Apologus/openLUXbox/docs/firmware/4Pong/4Pong.jpg

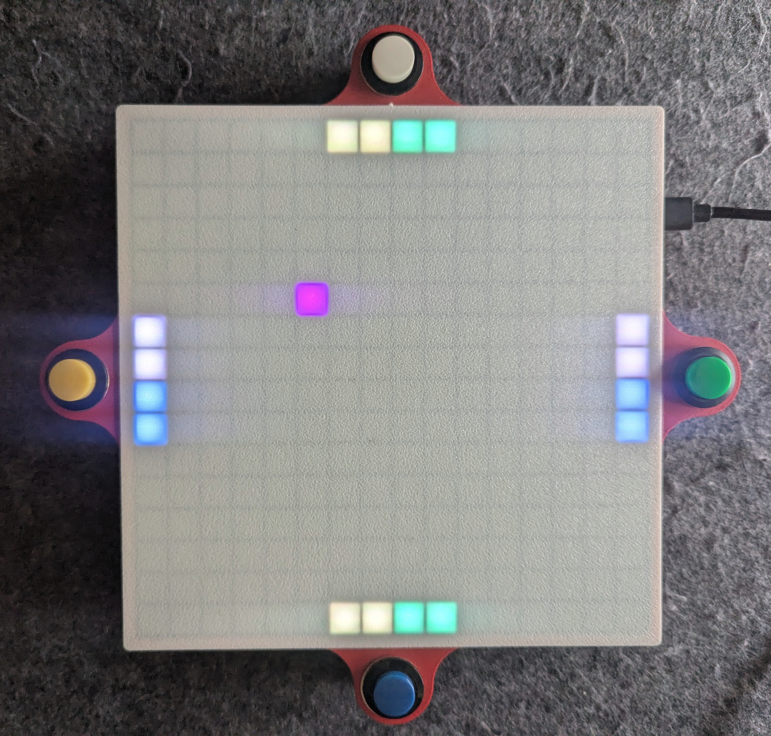
docs/firmware/4Pong/4Pong.jpg
