Apologus/openLUXbox/docs/firmware/canoLbalt/canoLbalt.jpg

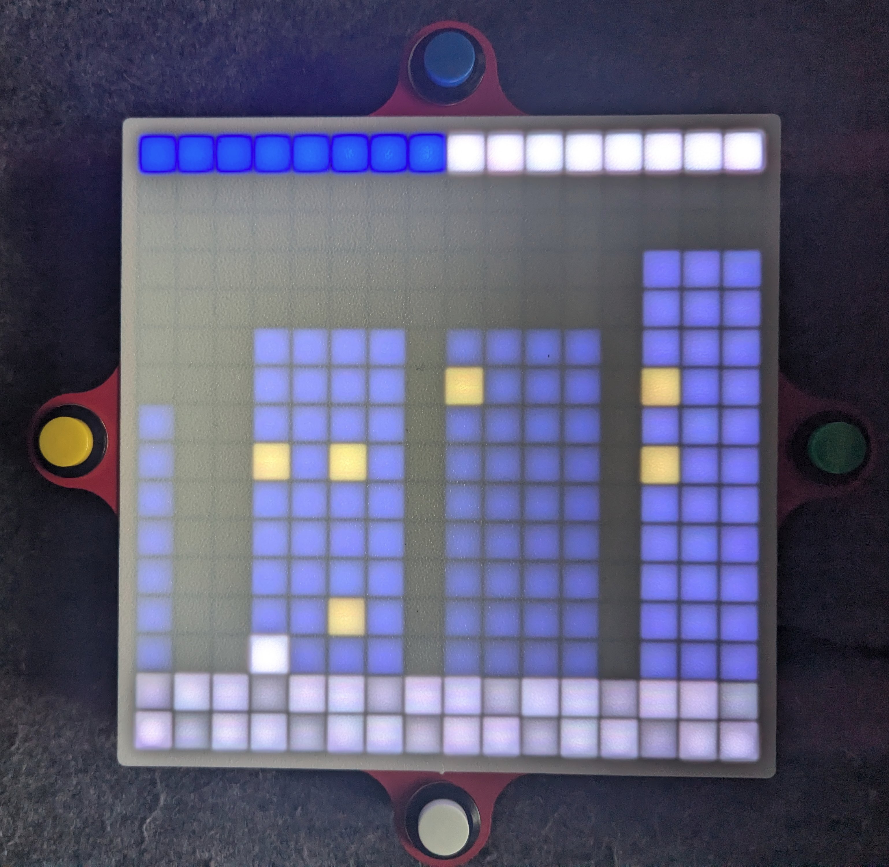
docs/firmware/canoLbalt/canoLbalt.jpg
