Apologus/openLUXbox/docs/firmware/Frog/Frog.jpg

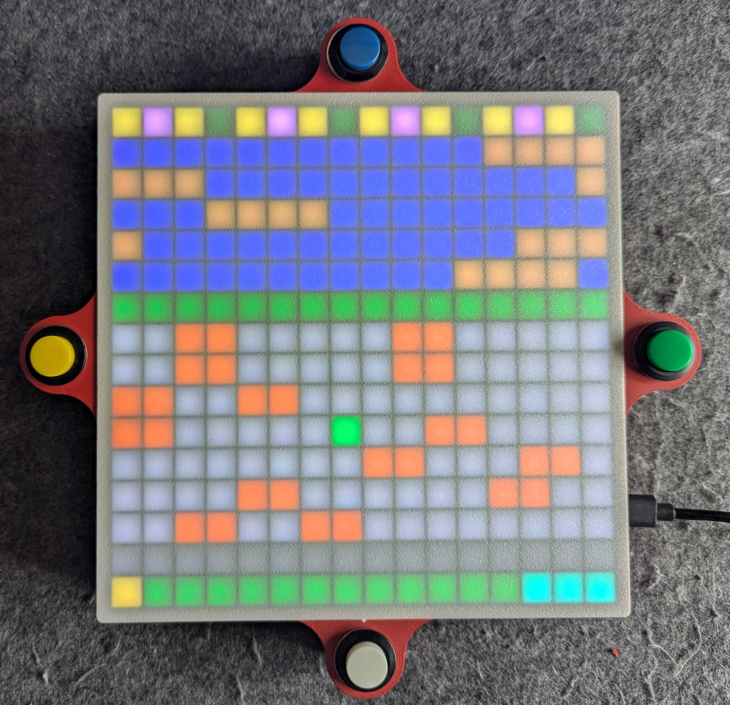
docs/firmware/Frog/Frog.jpg
