Apologus/openLUXbox/docs/firmware/Kreuzfeuer/Kreuzfeuer.jpg

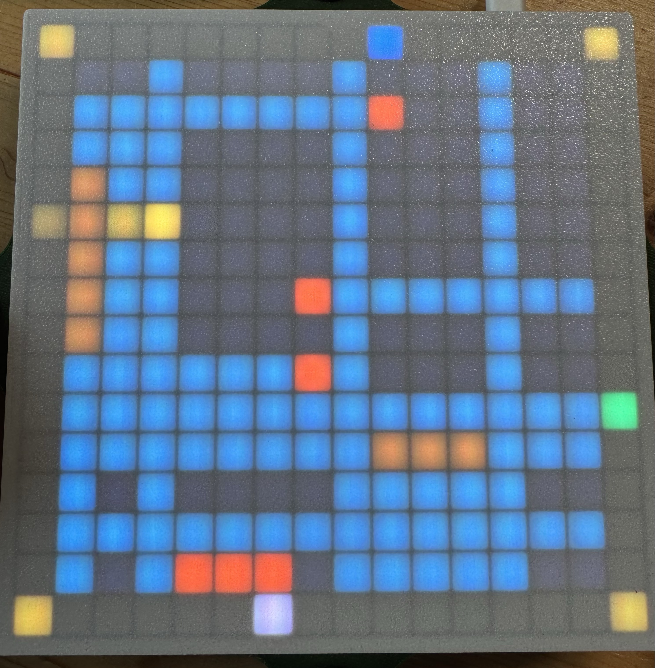
docs/firmware/Kreuzfeuer/Kreuzfeuer.jpg
