Apologus/openLUXbox/docs/firmware/Lux/Lux.jpg

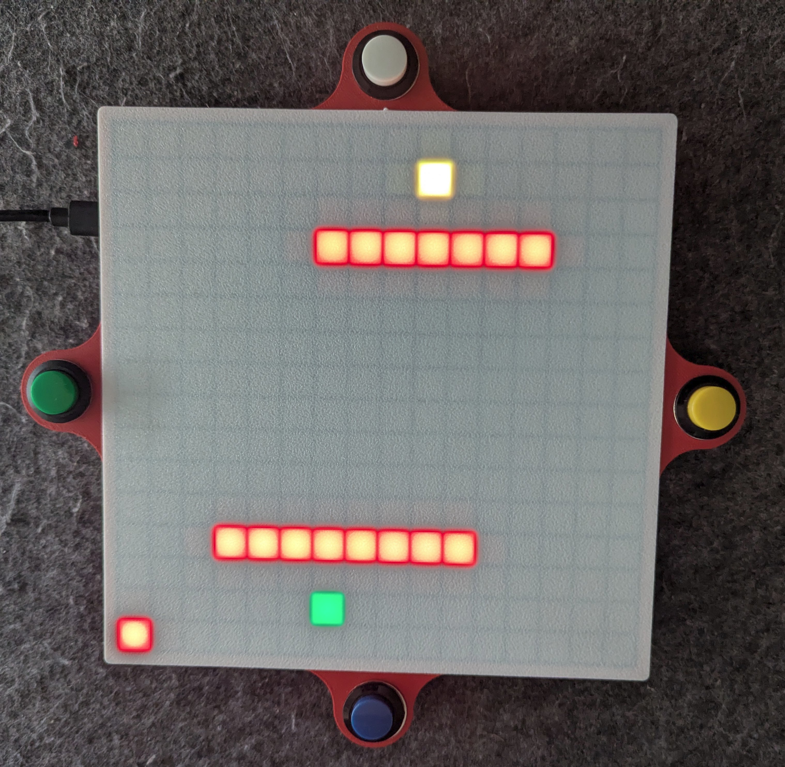
docs/firmware/Lux/Lux.jpg
