Apologus/openLUXbox/docs/firmware/Nano Hexagon/Nano Hexagon.jpg

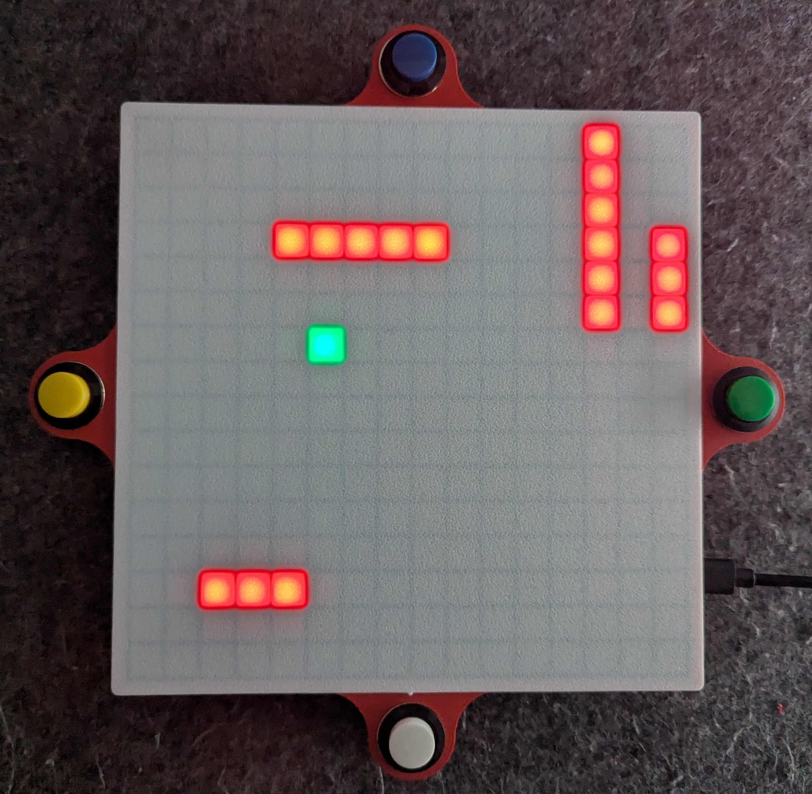
docs/firmware/Nano Hexagon/Nano Hexagon.jpg
