Apologus/openLUXbox/docs/firmware/Shining/Shining.jpg

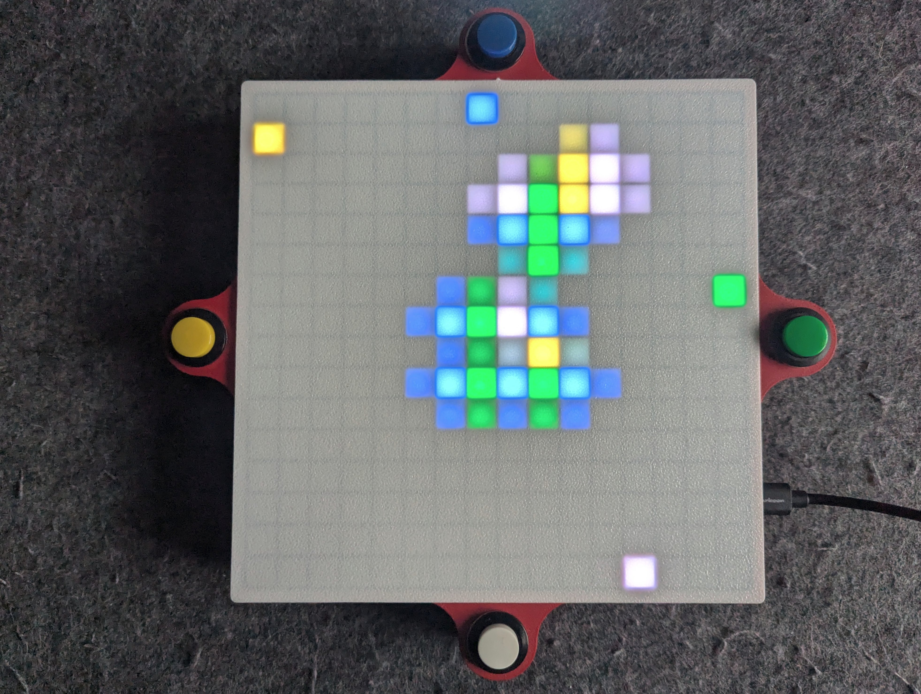
docs/firmware/Shining/Shining.jpg
