Apologus/openLUXbox/docs/firmware/Snake/Snake.jpg

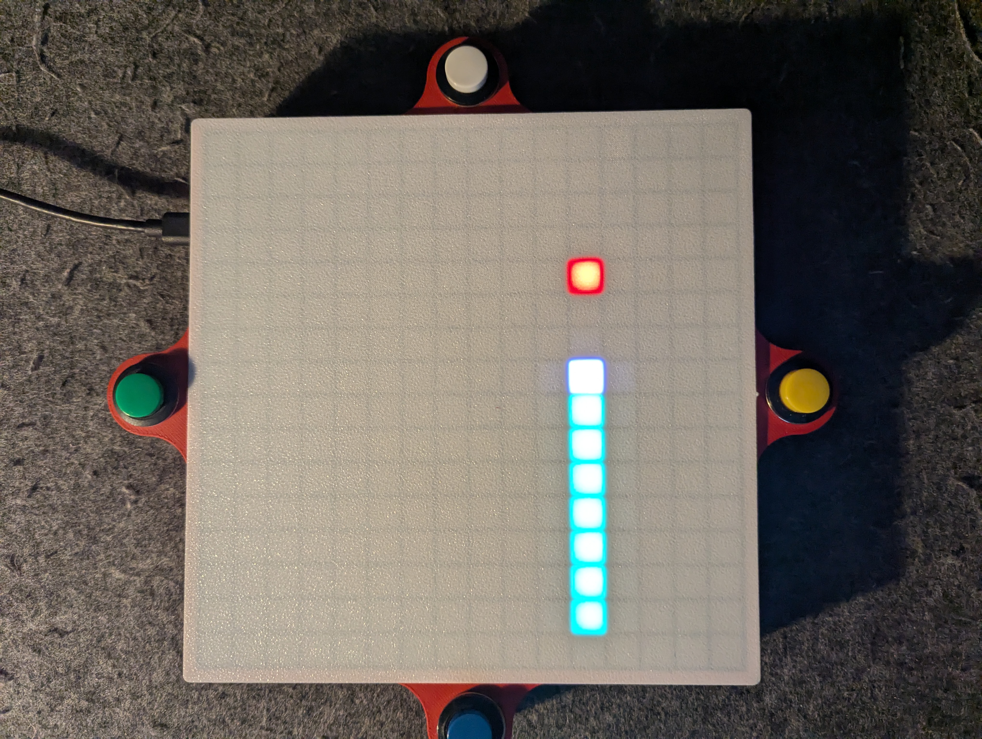
docs/firmware/Snake/Snake.jpg
