Apologus/openLUXbox/docs/openLUXbox.png

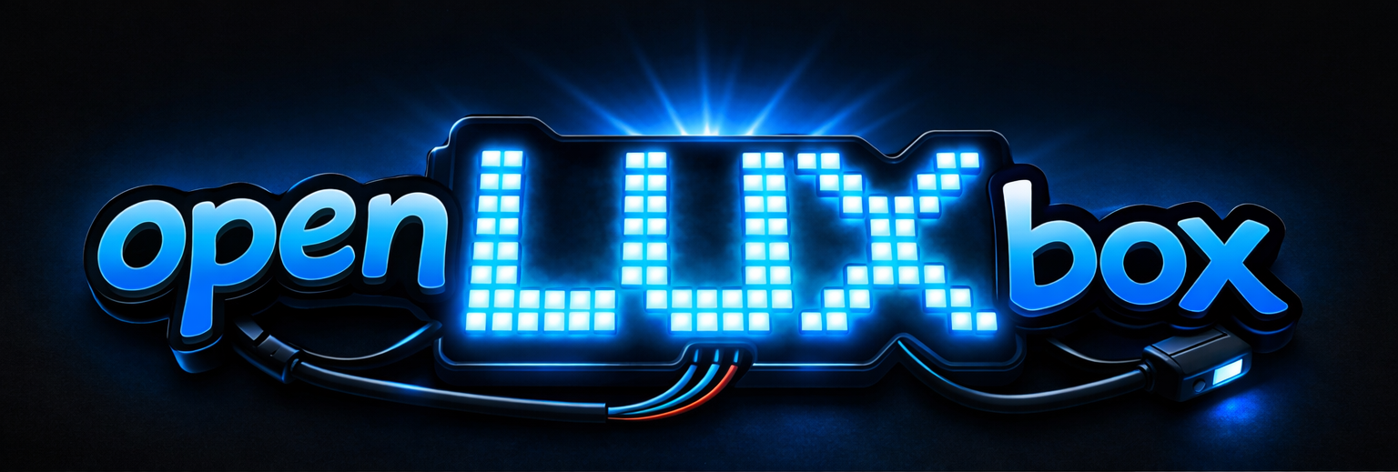
docs/openLUXbox.png
