Apologus/openLUXbox/Tech Specs/openLUXbox.kicad_sch

## KiCad design Tech Specs/openLUXbox.kicad_sch (2026-05-11)

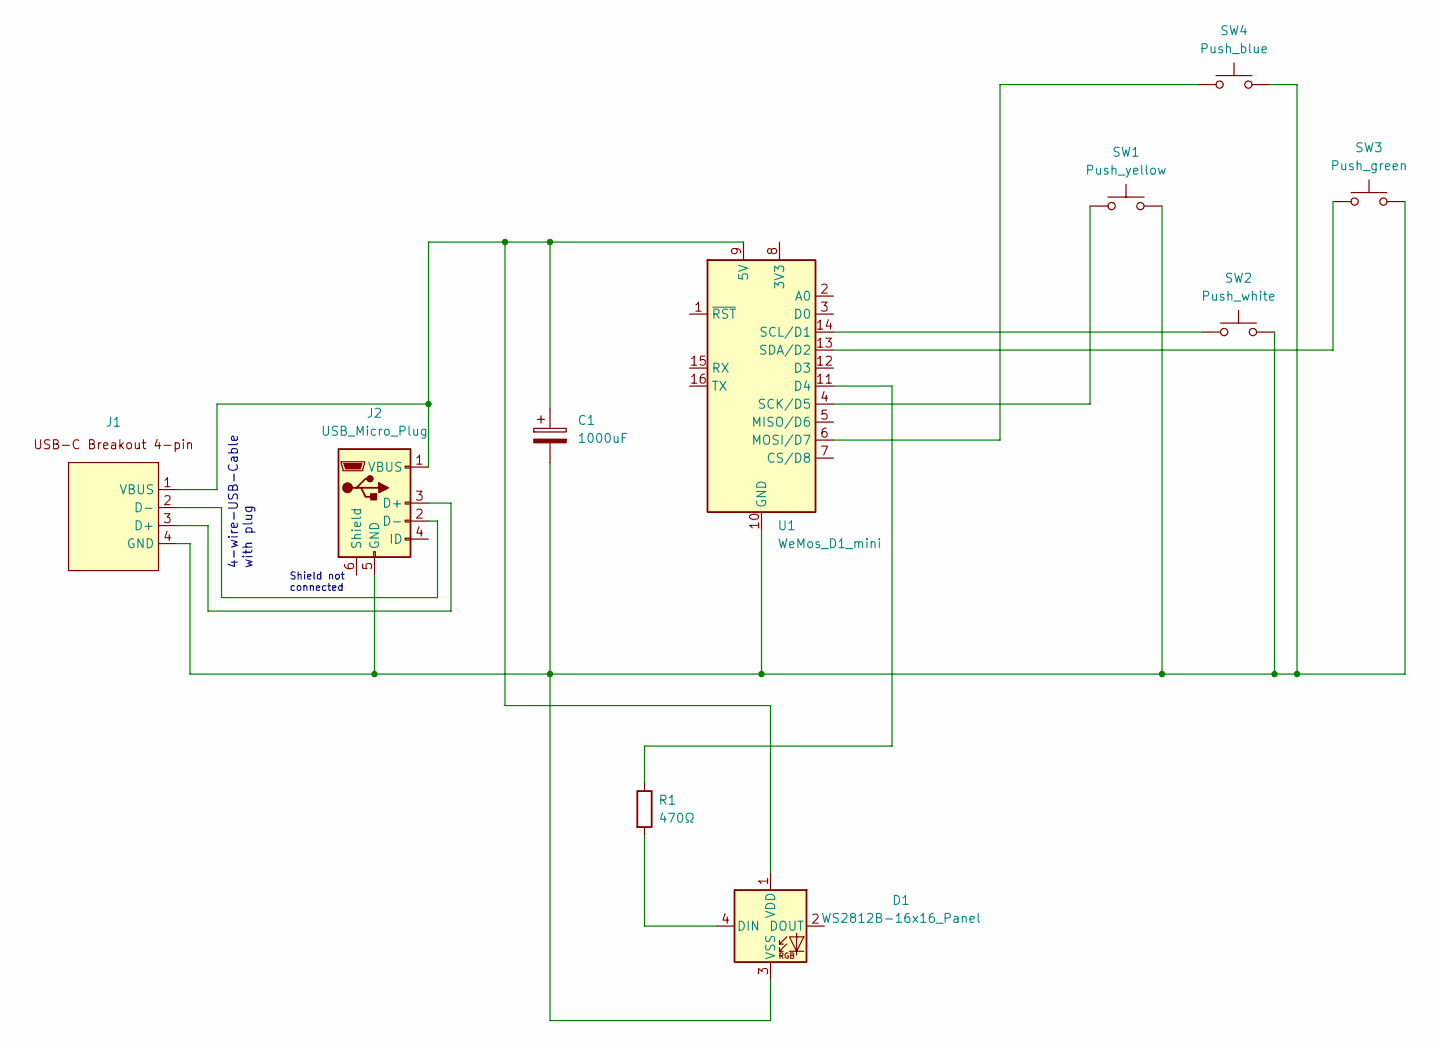
[picture p32: schematic openLUXbox.kicad_sch]

Parts:
C1: 1000uF
D1: WS2812B-16x16_Panel; LED_WS2812B_PLCC4_5.0x5.0mm_P3.2mm
J1: (no value)
J2: USB_Micro_Plug
R1: 470Ω
SW1: Push_yellow
SW2: Push_white
SW3: Push_green
SW4: Push_blue
U1: WeMos_D1_mini; WEMOS_D1_mini_light

Connections:
unnamed: C1.1, D1.1 (VDD), J1.1 (VBUS), J2.1 (VBUS), U1.9 (5V)
unnamed: C1.2, D1.3 (VSS), J1.4 (GND), J2.5 (GND), SW1.2, SW2.2, SW3.2, SW4.2, U1.10 (GND)
unnamed: D1.4 (DIN), R1.2
unnamed: J1.2 (D-), J2.2 (D-)
unnamed: J1.3 (D+), J2.3 (D+)
unnamed: R1.1, U1.11 (D4)
unnamed: SW1.1, U1.4 (SCK/D5)
unnamed: SW2.1, U1.14 (SCL/D1)
unnamed: SW3.1, U1.13 (SDA/D2)
unnamed: SW4.1, U1.6 (MOSI/D7)

Notes on the sheet:
4-wire-USB-Cable with plug
Shield not connected
